smartenough-org/smartenough/io-gate/src/message.rs

// Message parsing parts moved from io-ctrl. TODO: Maybe move to a shared crate.
use anyhow::bail;

use crate::consts::{InIdx, OutIdx, ProcIdx};

/* Generic CAN has 11-bit addresses.
 * - Messages must be unique
 * - Lower values have higher priorities.
 * - We want up to 64 devices on the bus.
 * - This gives 6 bit for device address and 5 for message type, ie. 32 different messages
 * TTTTTAAAAAA (T)ype + (A)ddress
 */

/// The lower the code, the more important the message on the CAN BUS.
mod msg_type {
    // Start with rare important events.
    // Range: 5 bits, 0x00 <-> 0x1f

    // 0 Reserved as invalid message
    // 1 Reserved for high-priority grouped type.

    /// Erroneous situation happened. Includes error code. See Info/Warning
    pub const ERROR: u8 = 0x02;

    // 3 reserved

    /// My output was changed, because of reasons.
    pub const OUTPUT_CHANGED: u8 = 0x04;
    /// My input was changed.
    pub const INPUT_TRIGGERED: u8 = 0x05;

    /// Set output X to Y (or invert state)
    pub const SET_OUTPUT: u8 = 0x08;
    /// Simulate input trigger, just like if the user presses the button.
    pub const TRIGGER_INPUT: u8 = 0x09;
    /// Call a predefined procedure in VM.
    pub const CALL_PROC: u8 = 0x0A;
    /// `Ping` of sorts.
    pub const REQUEST_STATUS: u8 = 0x0D;

    /// Periodic not triggered by an event status.
    pub const STATUS: u8 = 0x10;
    pub const TIME_ANNOUNCEMENT: u8 = 0x11;

    /// Similar to Error but with low priority.
    /// eg. Device started
    pub const INFO: u8 = 0x12;

    /*
    /// TODO: We will need something for OTA config updates.
    /// To whom this may concern (device ID), total length of OTA
    pub const MICROCODE_UPDATE_INIT: u8 = 0x1C;
    /// Part of binary code for upgrade.
    pub const MICROCODE_UPDATE_PART: u8 = 0x1A;
    /// CRC, apply if matches.
    pub const MICROCODE_UPDATE_END: u8 = 0x1B;
    */

    // 0x1F Reserved for low-priority grouped type
}

pub mod args {
    pub use anyhow::bail;
    pub use crate::consts::Trigger;

    #[derive(Clone, Copy, Debug)]
    #[repr(u16)]
    pub enum InfoCode {
        Started = 10,
    }

    #[derive(Clone, Copy, Debug)]
    #[repr(u8)]
    pub enum OutputState {
        Off = 0,
        On = 1,
        Toggle = 2,
        // on for x?
    }

    impl InfoCode {
        pub fn to_bytes(self) -> u16 {
            self as u16
        }
    }

    impl OutputState {
        pub fn to_bytes(self) -> u8 {
            self as u8
        }

        pub fn from_u8(raw: u8) -> anyhow::Result<Self> {
            match raw {
                0 => Ok(Self::Off),
                1 => Ok(Self::On),
                2 => Ok(Self::Toggle),
                _ => {
                    bail!("OutputState parsed from invalid arg {}", raw);
                }
            }
        }

        pub fn from_bool(on: bool) -> Self {
            if on {
                Self::On
            } else {
                Self::Off
            }
        }
    }

    impl Trigger {
        pub fn to_bytes(self) -> u8 {
            self as u8
        }

        pub fn from_u8(raw: u8) -> anyhow::Result<Self> {
            match raw {
                0 => Ok(Trigger::ShortClick),
                1 => Ok(Trigger::LongClick),
                2 => Ok(Trigger::Activated),
                3 => Ok(Trigger::Deactivated),
                4 => Ok(Trigger::LongActivated),
                5 => Ok(Trigger::LongDeactivated),
                _ => bail!("Invalid raw value {}, unable to convert to trigger", raw),
            }
        }
    }
}

/// This holds the decoded message internally.
#[derive(Debug)]
pub enum Message {
    // Start with rare important events.
    /// Erroneous situation happened. Includes error code.
    Error { code: u32 },
    /// Normal or slightly weird situation happened (eg. initialized)
    Info { code: u16, arg: u32 },

    /// My output was changed.
    OutputChanged {
        output: OutIdx,
        state: args::OutputState,
    },

    /// My output was changed.
    InputTriggered { input: InIdx },

    /// Request output change.
    /// 0 - deactivate, 1 - activate, 2 - toggle, * reserved (eg. time-limited setting)
    SetOutput {
        output: OutIdx,
        state: args::OutputState,
    },

    TriggerInput {
        input: InIdx,
        trigger: args::Trigger,
    },

    /// Ping. TODO: Handle RTR?
    RequestStatus,

    /// Periodic not triggered by event status.
    Status {
        uptime: u32,
        inputs: u16,
        outputs: u16,
    },

    /// Sent to endpoints.
    TimeAnnouncement {
        year: u16,
        month: u8,
        day: u8,
        hour: u8,
        minute: u8,
        second: u8,
        day_of_week: u8,
    },

    /// Call local procedure
    CallProcedure { proc_id: ProcIdx },
    /* TODO
    /// TODO: We will need something for OTA config updates.
    /// To whom this may concern (device ID), total length of OTA
    MicrocodeUpdateInit {
    addr: u8,
    length: u32,
    },
    /// Part of binary code for upgrade.
    MicrocodeUpdatePart {
    // Cycling offset.
    offset: u16,
    chunk: [u8; 6],
    },
    /// CRC, apply if matches.
    MicrocodeUpdateEnd {
    chunks: u16,
    length: u32,
    crc: u16,
    },
    /// Microcode received and applied.
    MicrocodeUpdateAck {
    length: u32,
    }
     */
}

/*
/// Holds decoded message with additional metadata.
Is it useful?
pub struct Envelope {
    // 5 bits
    raw_type: u8,
    // 6 bits
    addr: u8,
    // Decoded message
    message: Message,
}
*/

/// Raw message prepared for sending or just received.
#[derive(Default, Debug)]
pub struct MessageRaw {
    /// "Device" address - either source (for responses/status), or destination (for requests)
    addr: u8,
    msg_type: u8,

    length: u8,
    data: [u8; 8],
}

impl MessageRaw {
    pub fn from_bytes(addr: u8, msg_type: u8, data: &[u8]) -> Self {
        let mut raw = Self {
            addr,
            msg_type,
            length: data.len() as u8,
            data: [0; 8],
        };
        raw.data[0..data.len()].copy_from_slice(data);
        raw
    }

    /// Reconstruct from received data.
    pub fn from_can(can_addr: u16, data: &[u8]) -> Self {
        let (msg_type, addr) = Self::split_can_addr(can_addr);
        let mut raw = Self {
            addr,
            msg_type,
            length: data.len() as u8,
            data: [0; 8],
        };
        raw.data.copy_from_slice(data);
        raw
    }

    /// Combine parts into 11-bit CAN address.
    pub fn to_can_addr(&self) -> u16 {
        (self.msg_type as u16 & 0x1F) << 6 | (self.addr as u16 & 0x3F)
    }

    /// Split/parse 11 bit CAN address into msg type and device address
    pub fn split_can_addr(can_addr: u16) -> (u8, u8) {
        let device_addr: u8 = (can_addr & 0x3F).try_into().unwrap();
        let msg_type: u8 = ((can_addr >> 6) & 0x1F).try_into().unwrap();
        (msg_type, device_addr)
    }

    pub fn addr_type(&self) -> (u8, u8) {
        (self.addr, self.msg_type)
    }

    pub fn length(&self) -> u8 {
        self.length
    }

    pub fn data_as_array(&self) -> &[u8] {
        &self.data[0..self.length as usize]
    }
}

impl Message {
    pub fn from_raw(raw: MessageRaw) -> anyhow::Result<Self> {
        match raw.msg_type {
            msg_type::SET_OUTPUT => {
                if raw.length != 2 {
                    bail!("Set output has invalid message length {:?}", raw);
                } else {
                    let state = args::OutputState::from_u8(raw.data[1])?;
                    Ok(Message::SetOutput {
                        output: raw.data[0],
                        state,
                    })
                }
            }
            msg_type::TRIGGER_INPUT => {
                if raw.length != 2 {
                    bail!("Trigger input has an invalid message length {:?}", raw);
                } else {
                    let trigger = args::Trigger::from_u8(raw.data[1])?;
                    Ok(Message::TriggerInput {
                        input: raw.data[0],
                        trigger,
                    })
                }
            }
            msg_type::CALL_PROC => {
                if raw.length != 1 {
                    bail!("Call proc has invalid message length {:?}", raw);
                } else {
                    let proc_id: ProcIdx = raw.data[0];
                    Ok(Message::CallProcedure { proc_id })
                }
            }
            msg_type::TIME_ANNOUNCEMENT => {
                if raw.length != 2 + 1 + 1 + 1 + 1 + 1 + 1 {
                    bail!("Time announcement has invalid message length {:?}", raw);
                } else {
                    Ok(Message::TimeAnnouncement {
                        year: u16::from_le_bytes([raw.data[0], raw.data[1]]),
                        month: raw.data[2],
                        day: raw.data[3],
                        hour: raw.data[4],
                        minute: raw.data[5],
                        second: raw.data[6],
                        day_of_week: raw.data[7],
                    })
                }
            }

            msg_type::REQUEST_STATUS => Ok(Message::RequestStatus),

            msg_type::INFO | msg_type::ERROR | msg_type::STATUS => {
                bail!("Ignoring info/error/status message: {:?}", raw);
            }

            msg_type::OUTPUT_CHANGED | msg_type::INPUT_TRIGGERED => {
                bail!("Ignoring output/input change message {:?}", raw);
            }

            _ => {
                // TBH, probably safe to ignore.
                bail!("Unable to parse unhandled message type {:?}", raw);
            }
        }
    }

    /// Convert message to 11 bit address and up to 8 bytes of data to be sent via CAN.
    pub fn to_raw(&self, addr: u8) -> MessageRaw {
        let mut raw = MessageRaw{
            addr,
            .. MessageRaw::default()
        };

        match self {
            Message::Error { code } => {
                raw.msg_type = msg_type::ERROR;
                raw.length = 4;
                raw.data[0..4].copy_from_slice(&code.to_le_bytes());
            }
            Message::Info { code, arg } => {
                raw.msg_type = msg_type::INFO;
                raw.length = 6;
                raw.data[0..2].copy_from_slice(&code.to_le_bytes());
                raw.data[2..6].copy_from_slice(&arg.to_le_bytes());
            }
            Message::SetOutput { output, state } => {
                raw.msg_type = msg_type::SET_OUTPUT;
                raw.length = 2;
                raw.data[0] = *output;
                raw.data[1] = state.to_bytes();
            }
            Message::OutputChanged { output, state } => {
                raw.msg_type = msg_type::OUTPUT_CHANGED;
                raw.length = 2;
                raw.data[0] = *output;
                raw.data[1] = state.to_bytes();
            }
            Message::InputTriggered { input } => {
                raw.msg_type = msg_type::INPUT_TRIGGERED;
                raw.length = 1;
                raw.data[0] = *input; // ? More?
            }
            Message::Status {
                uptime,
                inputs,
                outputs,
            } => {
                raw.msg_type = msg_type::STATUS;
                raw.length = 8;
                raw.data[0..4].copy_from_slice(&uptime.to_le_bytes());
                raw.data[4..6].copy_from_slice(&inputs.to_le_bytes());
                raw.data[6..8].copy_from_slice(&outputs.to_le_bytes());
            }
            /* we only parse those.
            Message::TimeAnnouncement { year, month, day, hour, minute, second } => todo!(),
            Message::MicrocodeUpdateInit { addr, length } => todo!(),
            Message::MicrocodeUpdatePart { offset, chunk } => todo!(),
            Message::MicrocodeUpdateEnd { chunks, length, crc } => todo!(),
            Message::MicrocodeUpdateAck { length } => todo!(),
            */
            _ => {
                panic!("Not implemented message type conversion requested");
            }
        }

        raw
    }
}
